nalajcie/orienteering_clock/doc/insides_front.png

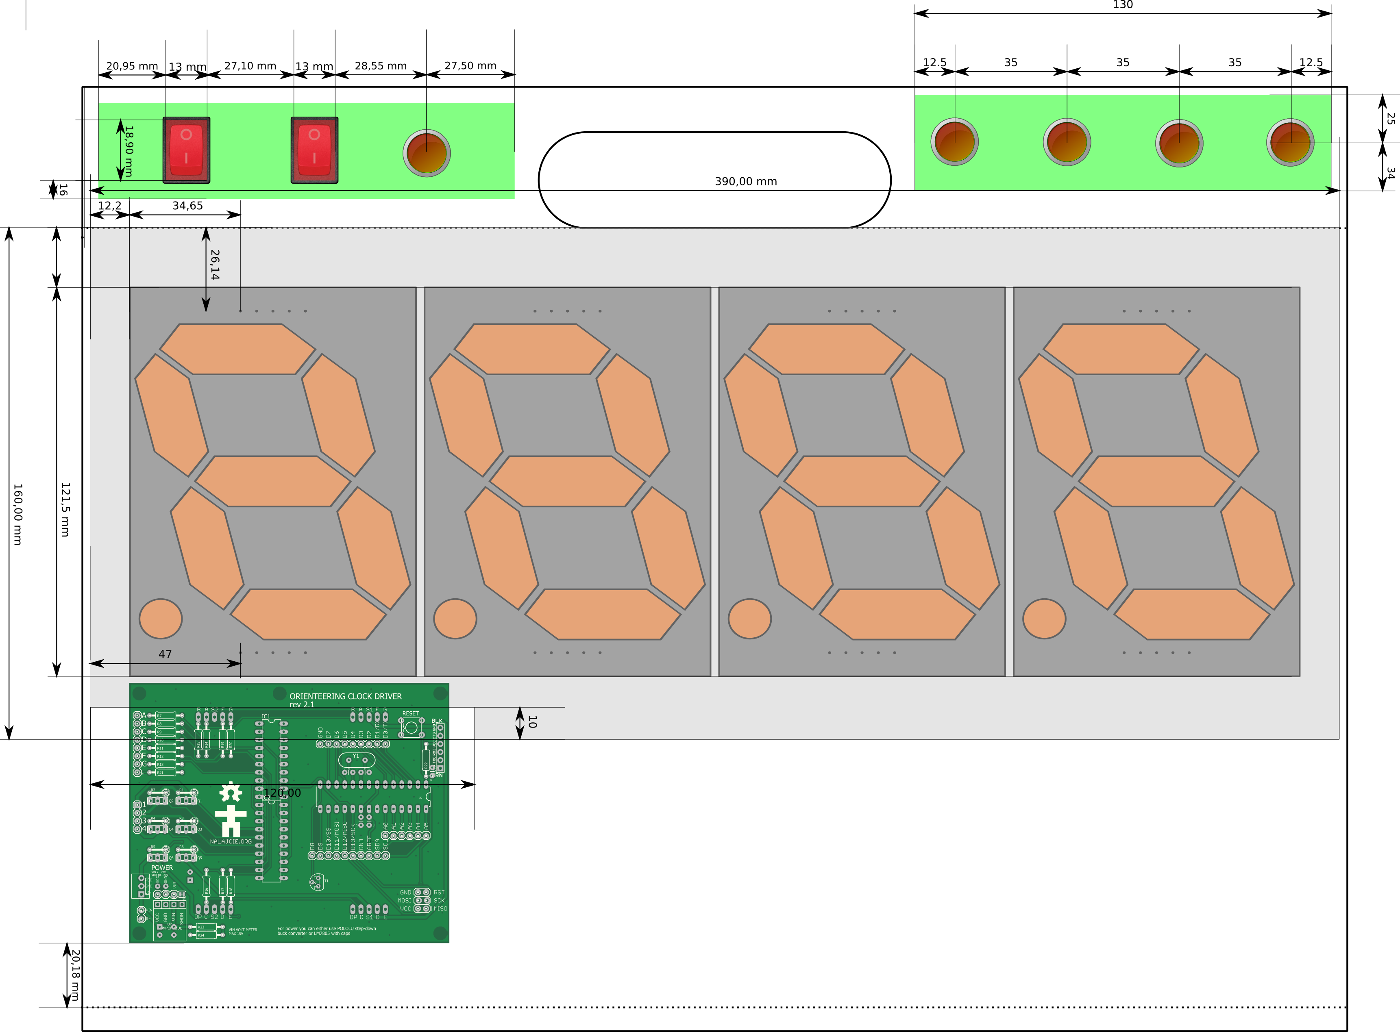
doc/insides_front.png
