nalajcie/orienteering_clock/schematics/v1.0/display_driver_board.png

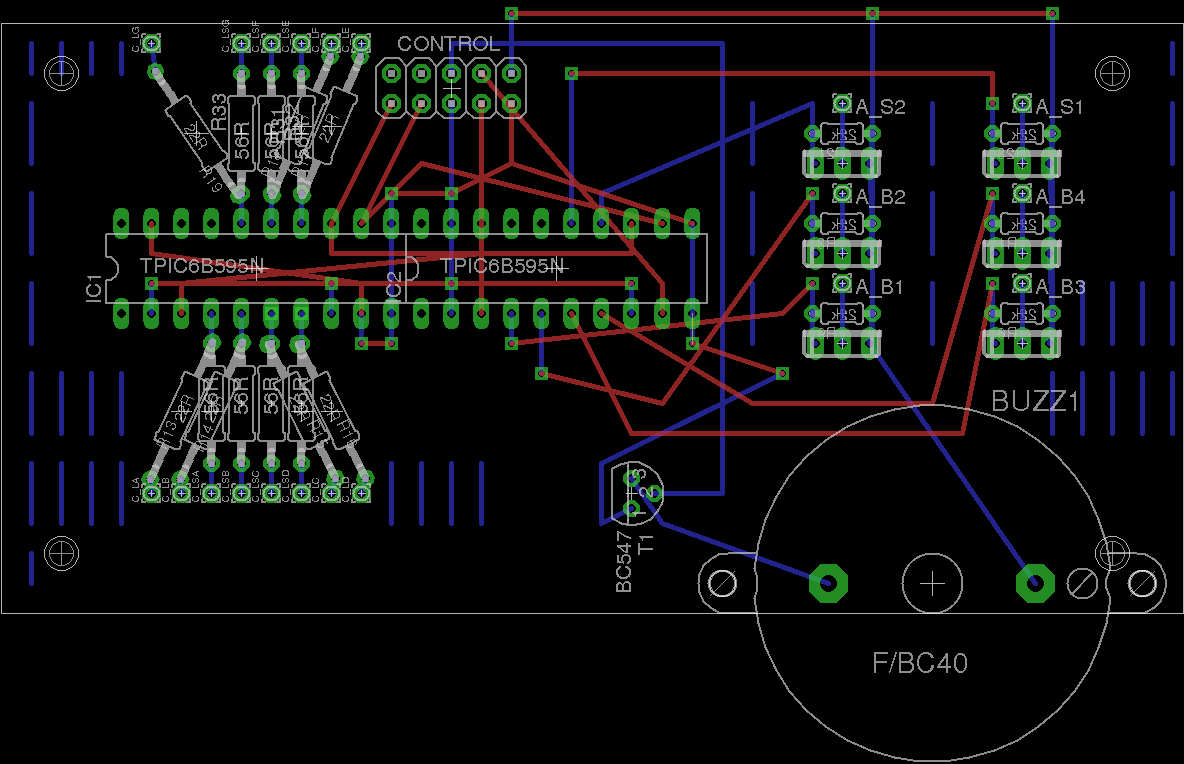
schematics/v1.0/display_driver_board.png
