nalajcie/orienteering_clock/schematics/examples/Arduino-Pro-Mini.brd

## EAGLE design schematics/examples/Arduino-Pro-Mini.brd (2014-11-30)


Parts:
C1, C2, C3, C10: 0.1uF; 0603-CAP
C13, C19: 10uF; EIA3216
D3: Green; 0603-LED-ALT1
FRAME1: FRAME-LETTER; CREATIVE_COMMONS
JP1: FTDI Basic; 1X06
JP2, JP3: M02PTH; 1X02
JP5, JP8: FIDUCIALUFIDUCIAL; MICRO-FIDUCIAL
JP6, JP7: M12PTH; 1X12
LED1: Red; 0603-LED-ALT1
Q1: 8/16/20MHz; RESONATOR-SMD-1:1
R1, R3: RESISTOR0603-RES; 0603-RES
R2, R11: 10K; 0603-RES
R6: 330; 0603-RES
S1: Reset; TACTILE-SWITCH-SMD-ALT01
SJ1: SOLDERJUMPERNC; SJ_2S
U1: ATMEGA328; TQFP32-08
U2: MIC5205; SOT23-5
U$1: LOGO-SFESK; SFE-LOGO-FLAME
U$3: OSHW-LOGOS; OSHW-LOGO-S
U$11: LOGO-SFENEW; SFE-NEW-WEBLOGO

Connections:
A0: JP6.8, U1.23 (PC0(ADC0))
A1: JP6.7, U1.24 (PC1(ADC1))
A2: JP6.6, U1.25 (PC2(ADC2))
A3: JP6.5, U1.26 (PC3(ADC3))
A4: JP2.1, R1.1, U1.27 (PC4(ADC4/SDA))
A5: JP2.2, R3.1, U1.28 (PC5(ADC5/SCL))
A6: JP3.1, U1.19 (ADC6)
A7: JP3.2, U1.22 (ADC7)
AREF: C1.2, U1.20 (AREF)
D2: JP7.8, U1.32 (PD2(INT0))
D3: JP7.7, U1.1 (PD3(INT1))
D4: JP7.6, U1.2 (PD4(XCK/T0))
D5: JP7.5, U1.9 (PD5(T1))
D6: JP7.4, U1.10 (PD6(AIN0))
D7: JP7.3, U1.11 (PD7(AIN1))
D8: JP7.2, U1.12 (PB0(ICP))
D9: JP7.1, U1.13 (PB1(OC1A))
D10: JP6.12, U1.14 (PB2(SS/OC1B))
DTR: C2.2, JP1.1 (DTR)
GND: C1.1, C3.1, C10.2, C13.C (-), C19.C (-), D3.C, JP1.5 (CTS), JP1.6 (GND), JP6.2, JP7.9, Q1.2, R11.1, S1.1, S1.2 (1), U1.3 (GND), U1.5 (AGND), U1.21 (GND), U2.2 (GND)
MISO: JP6.10, U1.16 (PB4(MISO))
MOSI: JP6.11, U1.15 (PB3(MOSI/OC2))
unnamed: Q1.3, U1.8 (PB7(XTAL2/TOSC2))
unnamed: Q1.1, U1.7 (PB6(XTAL1/TOSC1))
unnamed: LED1.A, SJ1.1, U2.5 (OUT)
unnamed: LED1.C, R11.2
unnamed: D3.A, R6.2
RAW: C19.A (+), JP6.1, U2.1 (IN), U2.3 (EN)
RESET: C2.1, JP6.3, JP7.10, R2.1, S1.3 (2), S1.4 (2), U1.29 (PC6(/RESET))
RXI: JP1.3 (TXO), JP7.11, U1.30 (PD0(RXD))
SCK: JP6.9, R6.1, U1.17 (PB5(SCK))
TXO: JP1.2 (RXI), JP7.12, U1.31 (PD1(TXD))
VCC: C3.2, C10.1, C13.A (+), JP1.4 (VCC), JP6.4, R1.2, R2.2, R3.2, SJ1.2, U1.4 (VCC), U1.6 (VCC), U1.18 (AVCC)

Notes on the sheet:
Original Arduino Mini Design by Team Arduino
Arduino Pro Mini Design by Spark Fun Electronics
Max Voltage Input: 16VDC
Max Current Output: 150mA
Board is marked with combination of
resonator frequency and regulator voltage.
VCC = 5V or 3.3V Output
Optional Pullups for I2C lines
Off Grid Breakout headers
Power isolation jumper
(for low power aplications)



Board: 2 copper layers, 17.8 x 33.0 mm, 29 parts (9 on the bottom side), 33 nets.
