nalajcie/orienteering_clock/schematics/examples/RGBW Controller31.brd

## EAGLE design schematics/examples/RGBW Controller31.brd (2014-11-30)

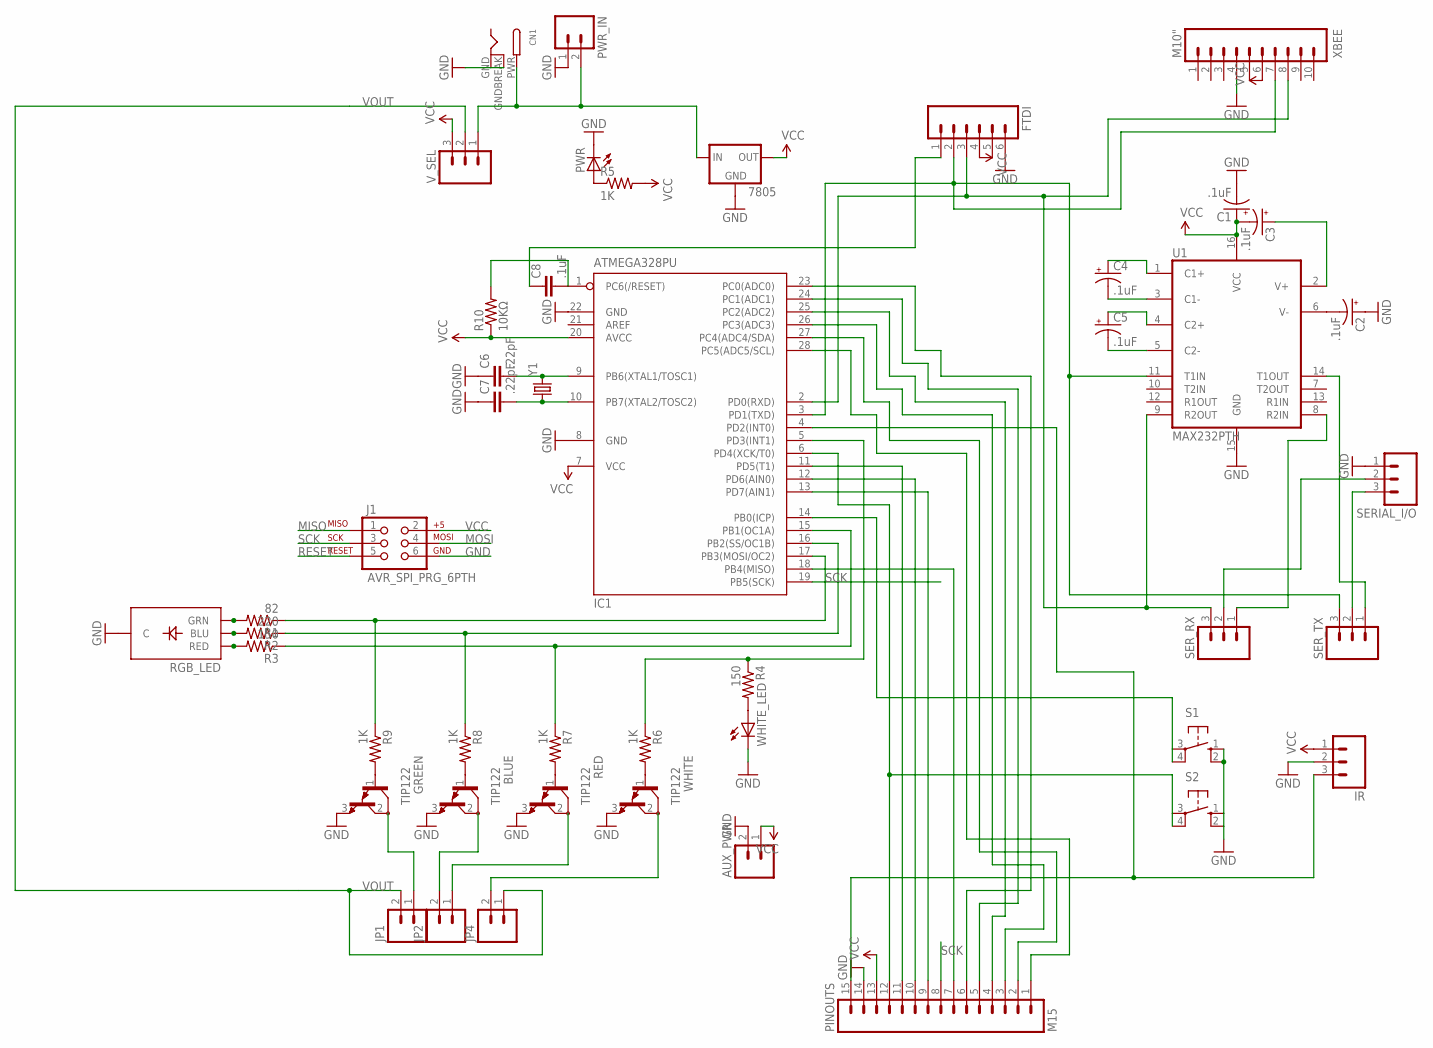
[picture p36: schematic RGBW Controller31.sch]

Parts:
7805: V_REG_78XXSIDE; 78XXL
AUX_PWR: M02PTH; 1X02
BLUE: TIP122; TO220
C1, C2, C3, C4, C5: .1uF; CPOL-RADIAL-100UF-25V
C6, C7: .22pF; CAP-PTH-SMALL
C8: .1uF; CAP-PTH-SMALL-KIT
CN1: DCBARRELPTH; DCJACK_2MM_PTH
FTDI: M06SIP; 1X06
GREEN: TIP122; TO220
IC1: ATMEGA328PU; DIL28-3
IR: M03PTH; 1X03
J1: AVR_SPI_PRG_6PTH; 2X3
JP1, JP2, JP4: M025MM; SCREWTERMINAL-5MM-2
PINOUTS: M15; 1X15
PWR: LED5MM
PWR_IN: M025MM; SCREWTERMINAL-5MM-2
R1: 82; AXIAL-0.4
R2: 220; AXIAL-0.4
R3, R4: 150; AXIAL-0.4
R5, R6, R7, R8, R9: 1K; AXIAL-0.4
R10: 10KΩ; AXIAL-0.4
RED: TIP122; TO220
RGB_LED: LED-TRICOLOR-THROUGHHOLE
S1, S2: 10-XX; B3F-10XX
SERIAL_I/O: M03SCREW; SCREWTERMINAL-3.5MM-3
SER_RX: M03PTH; 1X03
SER_TX: M03PTH; 1X03
U1: MAX232PTH; DIL16
V_SEL: M03PTH; 1X03
WHITE: TIP122; TO220
WHITE_LED: LED5MM
XBEE: M10"; 1X10
Y1: CRYSTALHC49US; HC49US

Connections:
GND: 7805.GND, AUX_PWR.2, BLUE.3 (E), C1.2 (-), C2.1 (+), C6.1, C7.1, CN1.GND, CN1.GNDBREAK, FTDI.6, GREEN.3 (E), IC1.8 (GND), IC1.22 (GND), IR.2, J1.6, PINOUTS.14, PWR.K (C), PWR_IN.1, RED.3 (E), RGB_LED.GND (C), S1.1 (S), S1.2 (S1), S2.1 (S), S2.2 (S1), SERIAL_I/O.1, U1.15 (GND), WHITE.3 (E), WHITE_LED.K (C), XBEE.4
MISO: IC1.18 (PB4(MISO)), J1.1, PINOUTS.7
MOSI: IC1.17 (PB3(MOSI/OC2)), J1.4, R1.P$1 (1), R9.P$1 (1)
unnamed: R1.P$2 (2), RGB_LED.GRN
unnamed: R2.P$2 (2), RGB_LED.BLU
unnamed: R3.P$2 (2), RGB_LED.RED
unnamed: R4.P$2 (2), WHITE_LED.A
unnamed: PWR.A, R5.P$1 (1)
unnamed: C5.1 (+), U1.4 (C2+)
unnamed: C4.2 (-), U1.3 (C1-)
unnamed: C4.1 (+), U1.1 (C1+)
unnamed: C5.2 (-), U1.5 (C2-)
unnamed: C3.1 (+), U1.2 (V+)
unnamed: C2.2 (-), U1.6 (V-)
unnamed: IC1.5 (PD3(INT1)), R4.P$1 (1), R6.P$1 (1)
unnamed: IC1.15 (PB1(OC1A)), R3.P$1 (1), R7.P$1 (1)
unnamed: IC1.16 (PB2(SS/OC1B)), R2.P$1 (1), R8.P$1 (1)
unnamed: C6.2, IC1.9 (PB6(XTAL1/TOSC1)), Y1.2
unnamed: C7.2, IC1.10 (PB7(XTAL2/TOSC2)), Y1.1
unnamed: IC1.4 (PD2(INT0)), IR.3, PINOUTS.15
unnamed: 7805.IN, CN1.PWR, PWR_IN.2, V_SEL.1
unnamed: GREEN.2 (C), JP1.1
unnamed: BLUE.2 (C), JP2.2
unnamed: JP2.1, RED.2 (C)
unnamed: JP4.2, WHITE.2 (C)
unnamed: IC1.14 (PB0(ICP)), S1.3, S1.4 (P1)
unnamed: C8.1, FTDI.1
unnamed: FTDI.2, IC1.3 (PD1(TXD)), SER_TX.3, U1.11 (T1IN), XBEE.7
unnamed: FTDI.3, IC1.2 (PD0(RXD)), SER_RX.3, U1.9 (R2OUT), XBEE.8
unnamed: IC1.13 (PD7(AIN1)), PINOUTS.9
unnamed: IC1.12 (PD6(AIN0)), PINOUTS.10
unnamed: IC1.11 (PD5(T1)), PINOUTS.11
unnamed: IC1.26 (PC3(ADC3)), PINOUTS.3
unnamed: IC1.27 (PC4(ADC4/SDA)), PINOUTS.2
unnamed: IC1.28 (PC5(ADC5/SCL)), PINOUTS.1
unnamed: IC1.6 (PD4(XCK/T0)), PINOUTS.12, S2.3, S2.4 (P1)
unnamed: IC1.25 (PC2(ADC2)), PINOUTS.4
unnamed: IC1.24 (PC1(ADC1)), PINOUTS.5
unnamed: IC1.23 (PC0(ADC0)), PINOUTS.6
unnamed: SERIAL_I/O.3, SER_TX.2
unnamed: SERIAL_I/O.2, SER_RX.2
unnamed: SER_TX.1, U1.14 (T1OUT)
unnamed: SER_RX.1, U1.8 (R2IN)
unnamed: R7.P$2 (2), RED.1 (B)
unnamed: BLUE.1 (B), R8.P$2 (2)
unnamed: GREEN.1 (B), R9.P$2 (2)
unnamed: R6.P$2 (2), WHITE.1 (B)
RESET: C8.2, IC1.1 (PC6(/RESET)), J1.5, R10.P$2 (2)
SCK: IC1.19 (PB5(SCK)), J1.3, PINOUTS.8
VCC: 7805.OUT, AUX_PWR.1, C1.1 (+), C3.2 (-), FTDI.4, IC1.7 (VCC), IC1.20 (AVCC), IR.1, J1.2, PINOUTS.13, R5.P$2 (2), R10.P$1 (1), U1.16 (VCC), V_SEL.3, XBEE.6
VOUT: JP1.2, JP4.1, V_SEL.2

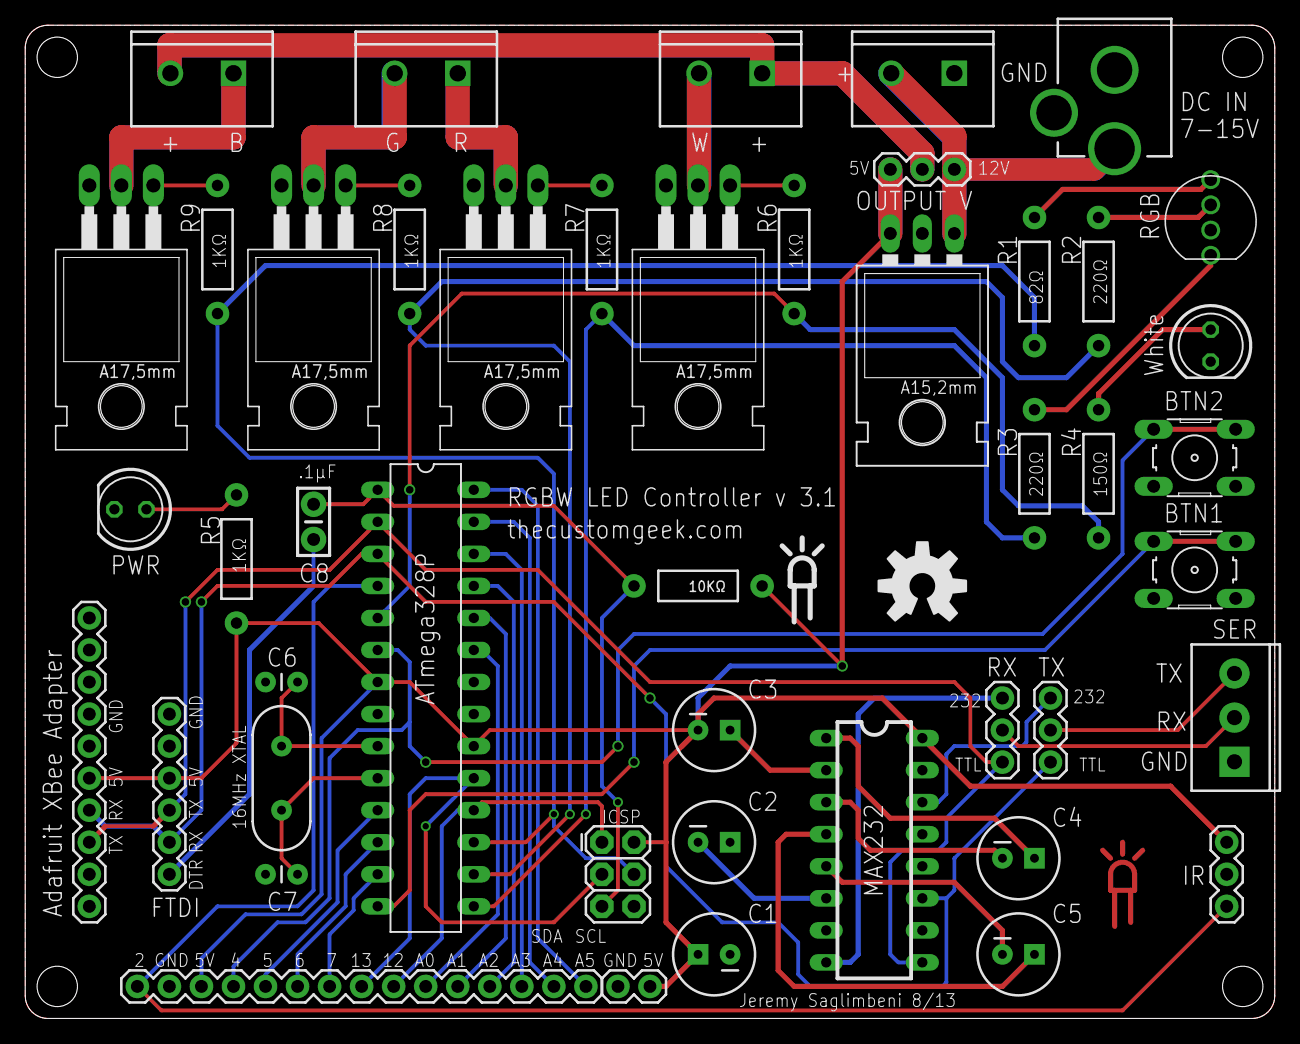
[picture p37: board RGBW Controller31.brd from above]

Board: 2 copper layers, 99.1 x 78.7 mm, 48 parts (1 on the bottom side), 51 nets.

Other parts of the board:
U$1, U$2: OSHW-LOGO-L
