nalajcie/orienteering_clock/schematics/examples/Serial-7-Segment-Shield.brd

## EAGLE design schematics/examples/Serial-7-Segment-Shield.brd (2014-11-30)

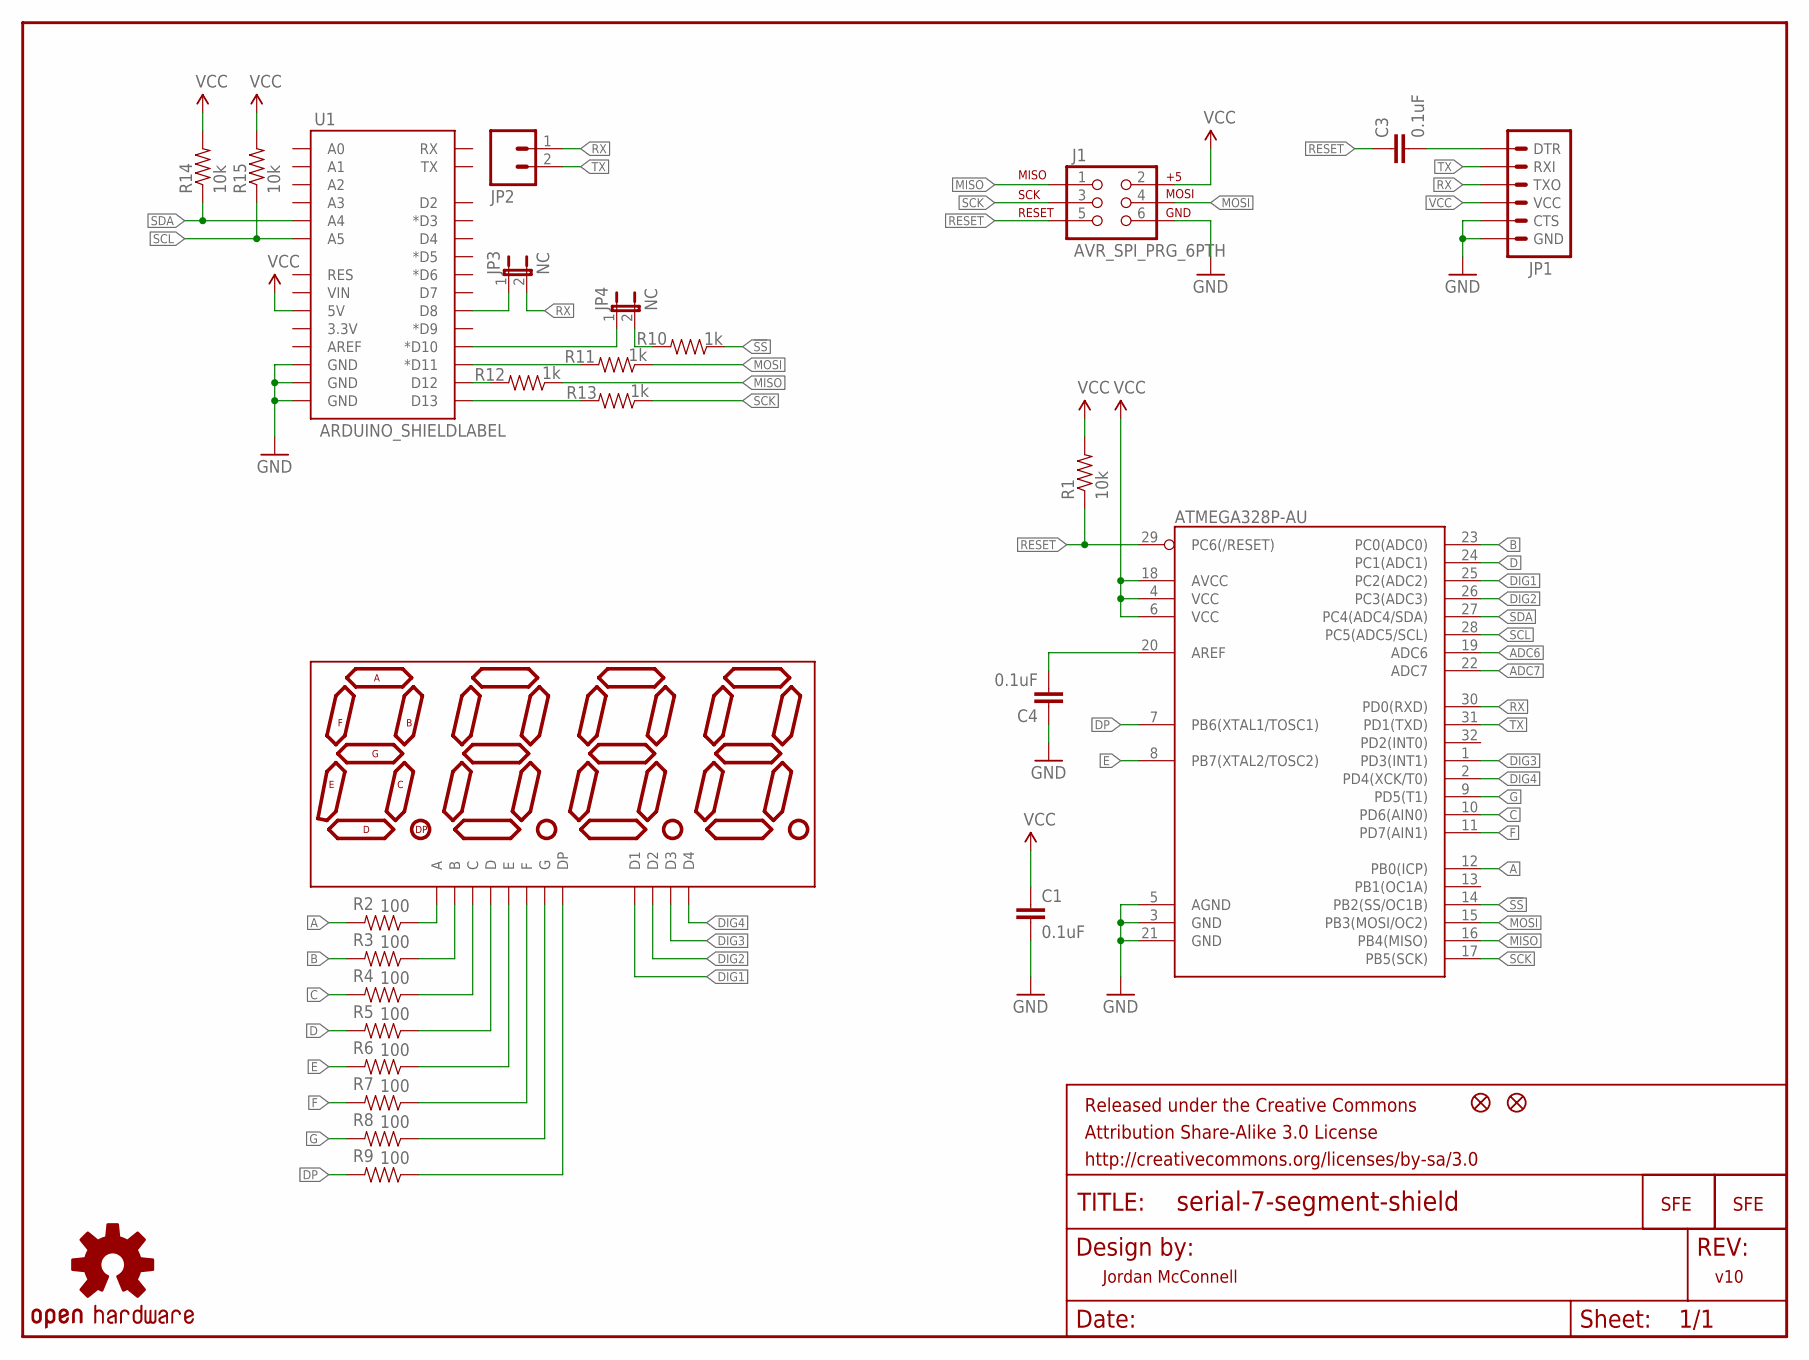
[picture p38: schematic Serial-7-Segment-Shield.sch]

Parts:
ATMEGA328P-AU: ATMEGA328P-AU; TQFP32-08
C1, C3, C4: 0.1uF; 0402-CAP
FRAME1: FRAME-LETTER; CREATIVE_COMMONS
J1: AVR_SPI_PRG_6PTH; 2X3
JP1: ARDUINO_SERIAL_PROGRAMPTH; 1X06
JP2: M02PTH; 1X02
JP3, JP4: NC; SJ_2S
JP9, JP10: FIDUCIALUFIDUCIAL; MICRO-FIDUCIAL
LOGO1, LOGO2: LOGO-SFENEW; SFE-NEW-WEBLOGO
R1, R14, R15: 10k; 0402-RES
R2, R3, R4, R5, R6, R7, R8, R9: 100; 0402-RES
R10, R11, R12, R13: 1k; 0402-RES
U1: ARDUINO_SHIELDLABEL; DUEMILANOVE_SHIELD
U$1: 7-SEGMENT-4DIGIT-COUNTERPTH; 7-SEGMENT-4DIGIT-COUNTER
U$4: OSHW-LOGOS; OSHW-LOGO-S

Connections:
!SS: ATMEGA328P-AU.14 (PB2(SS/OC1B)), R10.1
A: ATMEGA328P-AU.12 (PB0(ICP)), R2.2
ADC6: ATMEGA328P-AU.19 (ADC6)
ADC7: ATMEGA328P-AU.22 (ADC7)
B: ATMEGA328P-AU.23 (PC0(ADC0)), R3.2
C: ATMEGA328P-AU.10 (PD6(AIN0)), R4.2
D: ATMEGA328P-AU.24 (PC1(ADC1)), R5.2
DIG1: ATMEGA328P-AU.25 (PC2(ADC2)), U$1.12 (D1)
DIG2: ATMEGA328P-AU.26 (PC3(ADC3)), U$1.9 (D2)
DIG3: ATMEGA328P-AU.1 (PD3(INT1)), U$1.8 (D3)
DIG4: ATMEGA328P-AU.2 (PD4(XCK/T0)), U$1.6 (D4)
DP: ATMEGA328P-AU.7 (PB6(XTAL1/TOSC1)), R9.2
E: ATMEGA328P-AU.8 (PB7(XTAL2/TOSC2)), R6.2
F: ATMEGA328P-AU.11 (PD7(AIN1)), R7.2
G: ATMEGA328P-AU.9 (PD5(T1)), R8.2
GND: ATMEGA328P-AU.3 (GND), ATMEGA328P-AU.5 (AGND), ATMEGA328P-AU.21 (GND), C1.2, C4.1, J1.6, JP1.5 (CTS), JP1.6 (GND), U1.GND@0 (GND), U1.GND@1 (GND), U1.GND@2 (GND)
MISO: ATMEGA328P-AU.16 (PB4(MISO)), J1.1, R12.1
MOSI: ATMEGA328P-AU.15 (PB3(MOSI/OC2)), J1.4, R11.1
unnamed: ATMEGA328P-AU.20 (AREF), C4.2
unnamed: R13.2, U1.D13
unnamed: R12.2, U1.D12
unnamed: R11.2, U1.D11 (*D11)
unnamed: JP4.2, R10.2
unnamed: JP4.1, U1.D10 (*D10)
unnamed: JP3.1, U1.D8
unnamed: R2.1, U$1.11 (A)
unnamed: R3.1, U$1.7 (B)
unnamed: C3.2, JP1.1 (DTR)
unnamed: R4.1, U$1.4 (C)
unnamed: R5.1, U$1.2 (D)
unnamed: R6.1, U$1.1 (E)
unnamed: R7.1, U$1.10 (F)
unnamed: R8.1, U$1.5 (G)
unnamed: R9.1, U$1.3 (DP)
RESET: ATMEGA328P-AU.29 (PC6(/RESET)), C3.1, J1.5, R1.1
RX: ATMEGA328P-AU.30 (PD0(RXD)), JP1.3 (TXO), JP2.1, JP3.2
SCK: ATMEGA328P-AU.17 (PB5(SCK)), J1.3, R13.1
SCL: ATMEGA328P-AU.28 (PC5(ADC5/SCL)), R15.1, U1.A5
SDA: ATMEGA328P-AU.27 (PC4(ADC4/SDA)), R14.1, U1.A4
TX: ATMEGA328P-AU.31 (PD1(TXD)), JP1.2 (RXI), JP2.2
VCC: ATMEGA328P-AU.4 (VCC), ATMEGA328P-AU.6 (VCC), ATMEGA328P-AU.18 (AVCC), C1.1, J1.2, JP1.4 (VCC), R1.2, R14.2, R15.2, U1.5V

Notes on the sheet:
Jordan McConnell
v10

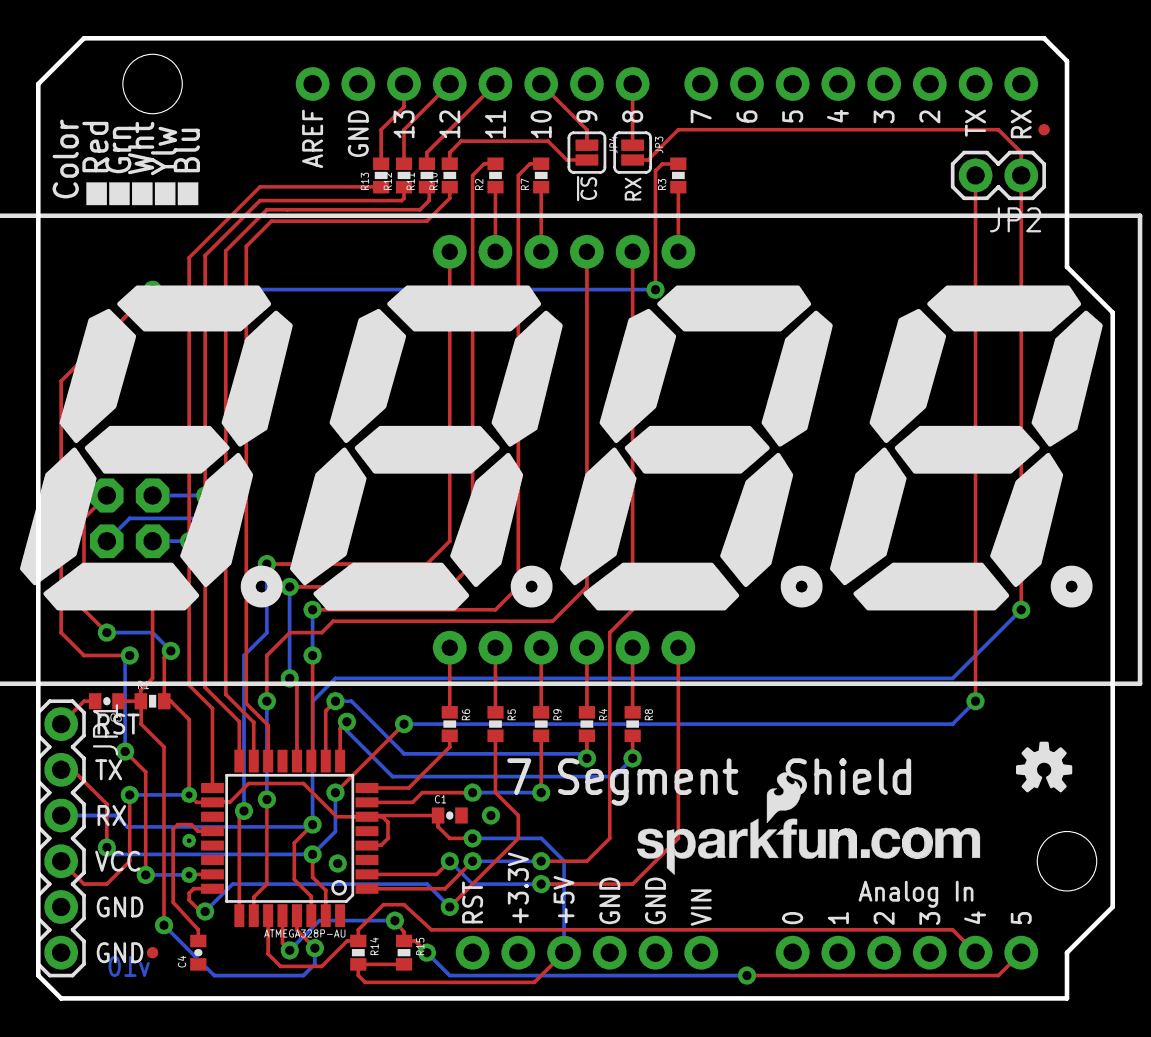
[picture p39: board Serial-7-Segment-Shield.brd from above]

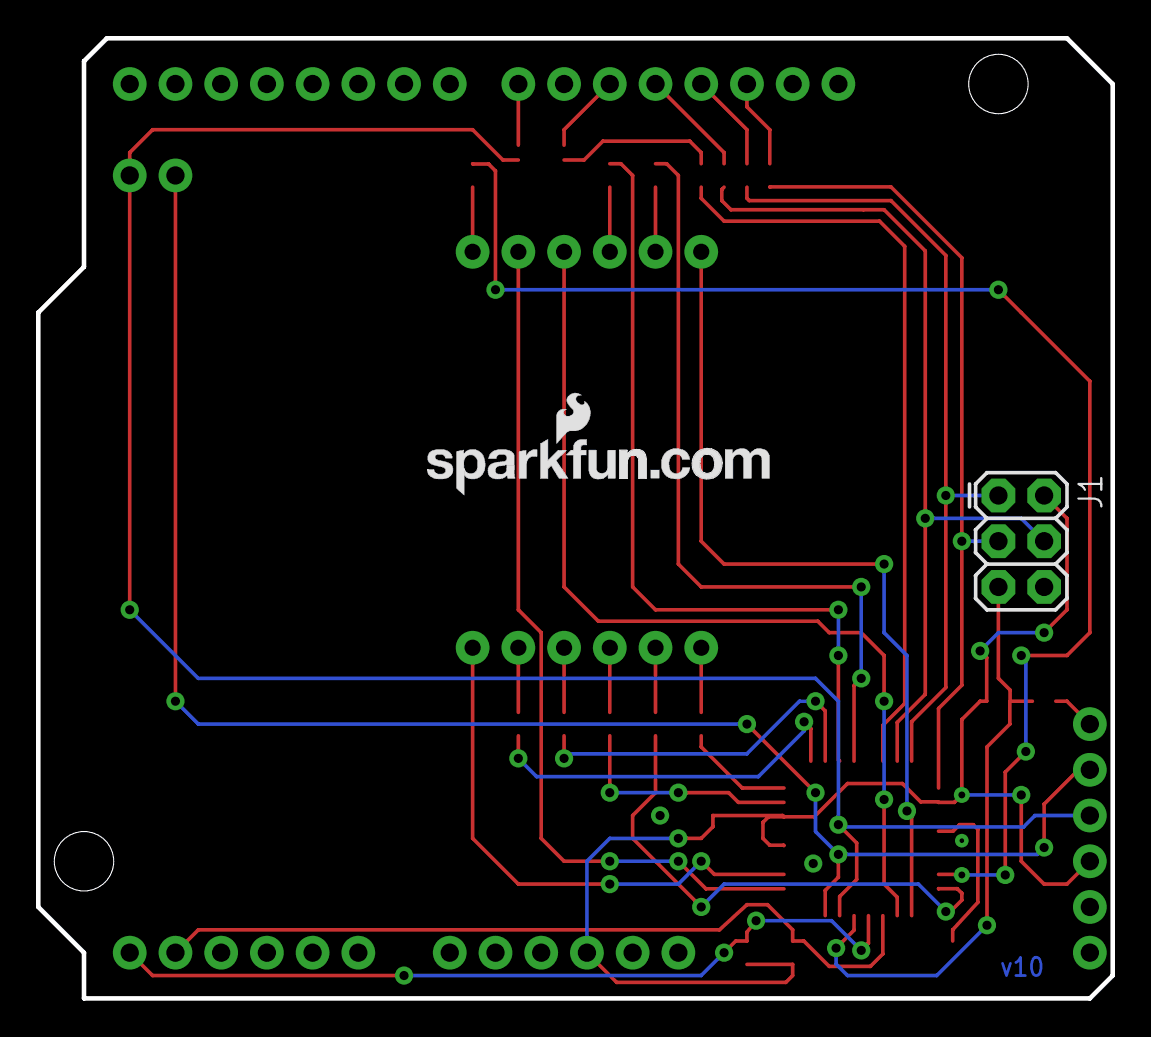
[picture p40: board Serial-7-Segment-Shield.brd from below]

Board: 2 copper layers, 59.7 x 53.3 mm, 32 parts (2 on the bottom side), 39 nets.
