nalajcie/orienteering_clock/src/hw.h

/* hardware pinout connection defines. May change with hardware revision */
#ifndef _HW_H
#define _HW_H

#define CURR_HW_REVISION        2



#if CURR_HW_REVISION == 1
/***** Arduino UNO Rev 3 ******/
#define DISPLAY_G_PIN            9 /* for quickly holding every output of high-side driver LOW */
#define DISPLAY_LATCH_PIN       10 /* also SPISS port */

/* buzzer */
#define BUZZ_CTL                3

/* handled automatically by SPI library */
#define DISPLAY_SPI_MOSI_PIN    11
#define UNUSED_SPI_MISO_PIN     12
#define DISPLAY_SPI_SCK_PIN     13

/* buttons - the analog 0-3 pins are also known as 14-17 */
#define BUTTON_SET              14
#define BUTTON_UP               15
#define BUTTON_DOWN             16
#define BUTTON_MODE             17

/* indexes in the table */
#define BUTTON_UP_IDX           0
#define BUTTON_DOWN_IDX         1
#define BUTTON_SET_IDX          2
#define BUTTON_MODE_IDX         3

#elif CURR_HW_REVISION == 2
/***** Orienteering clock driver rev 2.0 ******/

/* features */
#define HAS_BUTTON_BATT         // additional button
#define HAS_VIN_SENSE           // ability to sense VIN voltage
#define BUG_INVERTED_SMALL_DISPLAYS  // S1 <->S2 mixed up :(

#define DISPLAY_G_PIN            9 /* for quickly holding every output of high-side driver LOW */
#define DISPLAY_LATCH_PIN       10 /* also SPI SS port */

#define VIN_SENSE_PIN           14 /* A0 */

/* buzzer */
#define BUZZ_CTL                8

/* handled automatically by SPI library */
#define DISPLAY_SPI_MOSI_PIN    11
#define UNUSED_SPI_MISO_PIN     12
#define DISPLAY_SPI_SCK_PIN     13

/* buttons - D3-D7 (D0-D1 - TX/RX) */
#define BUTTON_SET              3
#define BUTTON_UP               4
#define BUTTON_DOWN             5
#define BUTTON_MODE             6
#define BUTTON_BATT             7

/* indexes in the table */
#define BUTTON_UP_IDX           0
#define BUTTON_DOWN_IDX         1
#define BUTTON_SET_IDX          2
#define BUTTON_MODE_IDX         3
#define BUTTON_BATT_IDX         4

#endif // CURR_HW_REVISION


#endif // _HW_H
